ryuzakikami/bll_chess_game/docs/HausarbeitBLL/res/20250331_210004.jpg

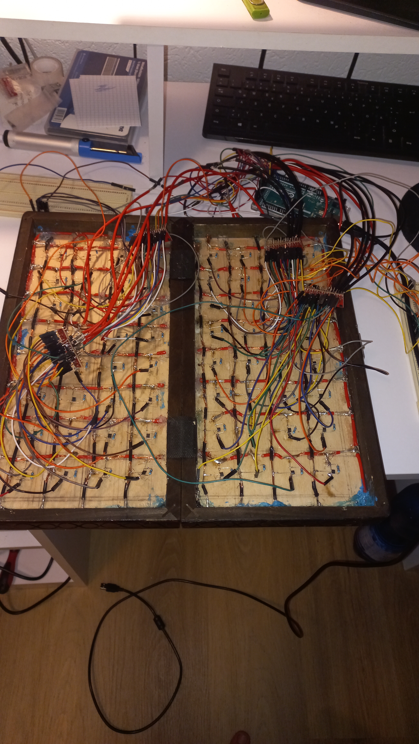
docs/HausarbeitBLL/res/20250331_210004.jpg
