ryuzakikami/bll_chess_game/docs/HausarbeitBLL/res/20250401_221237.jpg

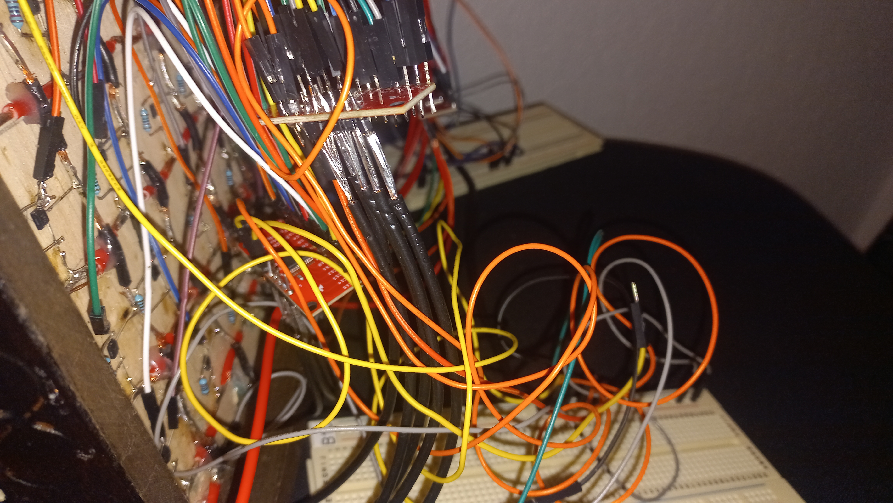
docs/HausarbeitBLL/res/20250401_221237.jpg
