ryuzakikami/bll_chess_game/docs/HausarbeitBLL/res/20250401_221310.jpg

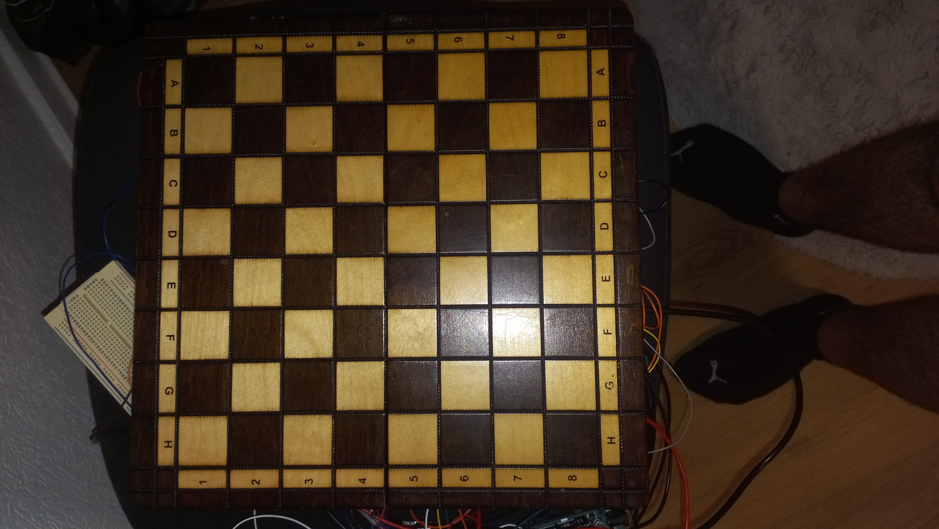
docs/HausarbeitBLL/res/20250401_221310.jpg
