ryuzakikami/bll_chess_game/docs/HausarbeitBLL/res/20250401_221319.jpg

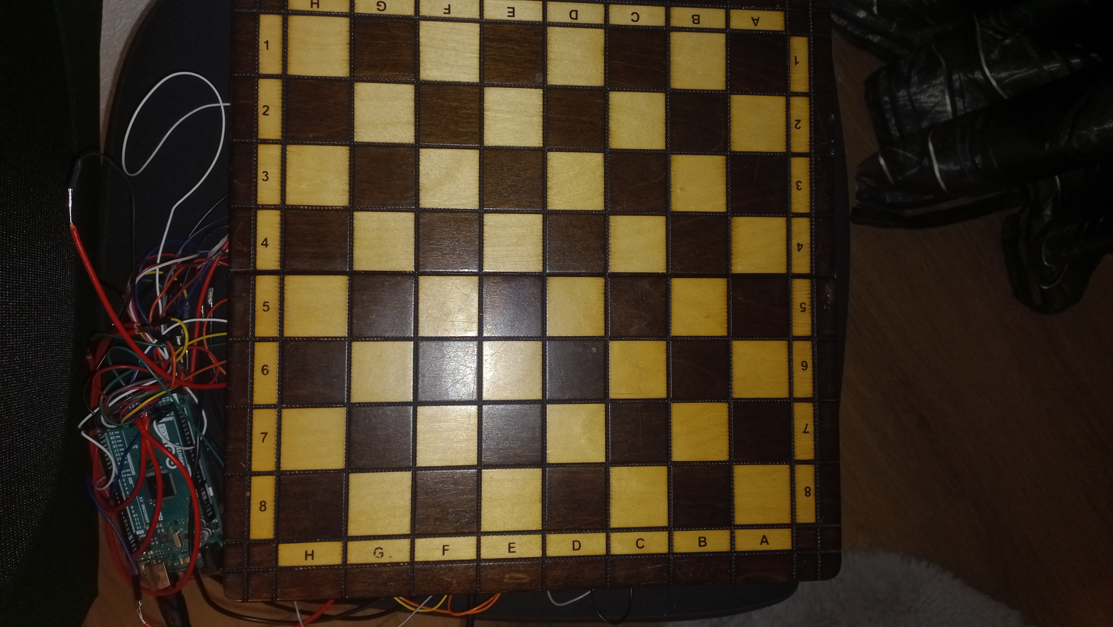
docs/HausarbeitBLL/res/20250401_221319.jpg
