ryuzakikami/bll_chess_game/docs/HausarbeitBLL/res/Elektronik/3144-Hall-Sensor.png

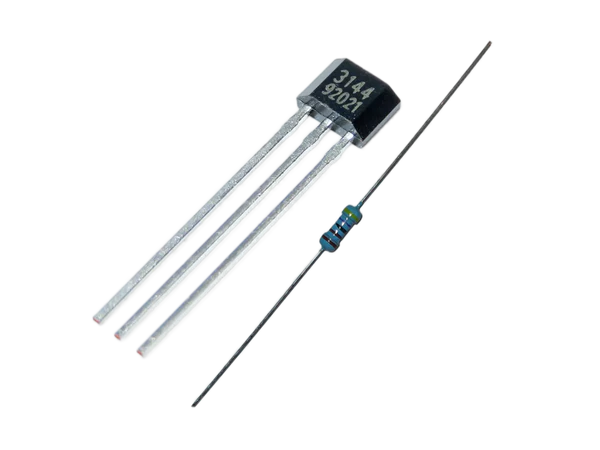
docs/HausarbeitBLL/res/Elektronik/3144-Hall-Sensor.png
