ryuzakikami/bll_chess_game/docs/HausarbeitBLL/res/Elektronik/Ardiono_mega_echt.png

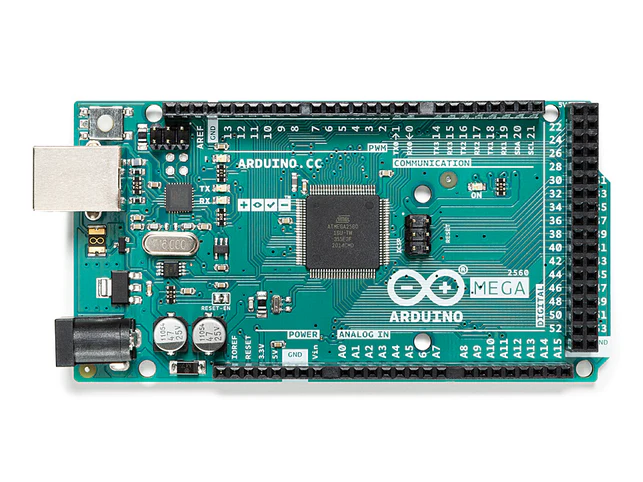
docs/HausarbeitBLL/res/Elektronik/Ardiono_mega_echt.png
