ryuzakikami/bll_chess_game/docs/HausarbeitBLL/res/Logic-Circuit-of-16-to-1-MUX.jpg.png

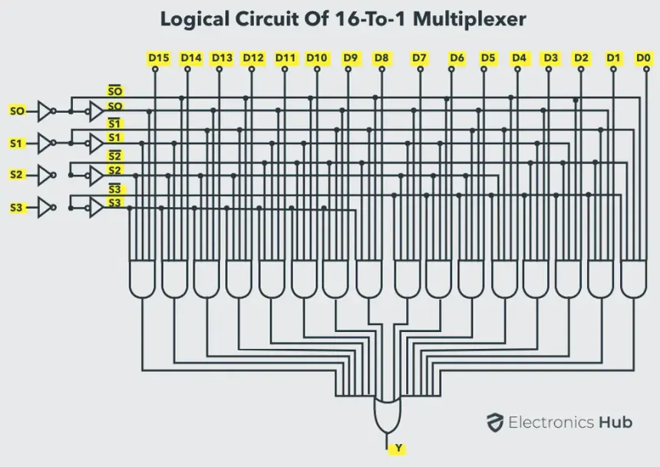
docs/HausarbeitBLL/res/Logic-Circuit-of-16-to-1-MUX.jpg.png
