ryuzakikami/bll_chess_game/docs/HausarbeitBLL/res/Vermessen.jpg

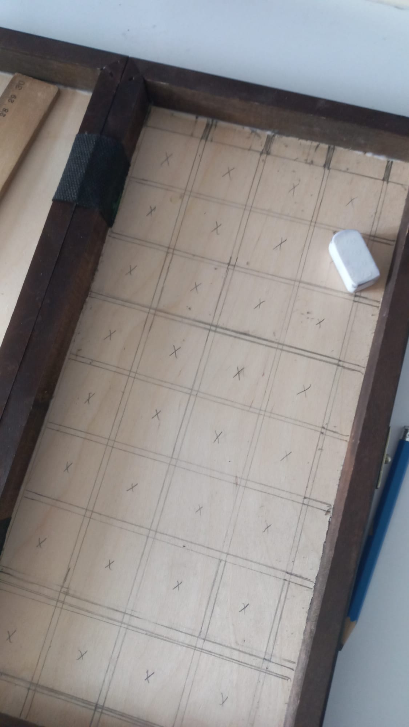
docs/HausarbeitBLL/res/Vermessen.jpg
