ryuzakikami/bll_chess_game/docs/schachbrett_model/Full Chess set (With 3D Board!) - 6810813/images/Untitled_7.png

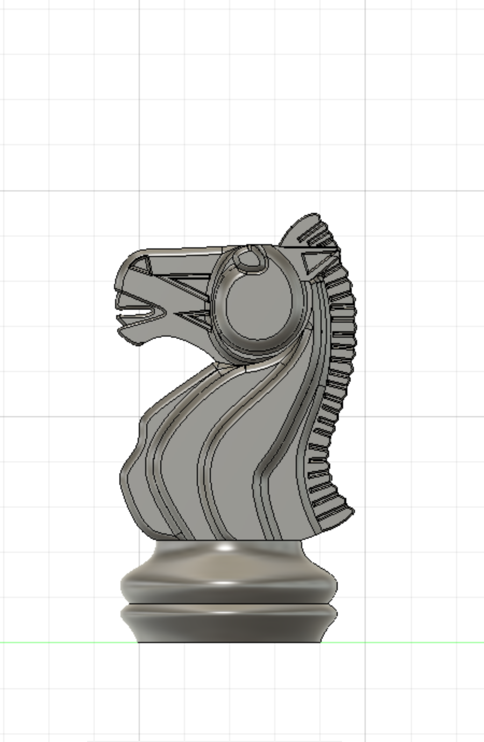
docs/schachbrett_model/Full Chess set (With 3D Board!) - 6810813/images/Untitled_7.png
