ryuzakikami/bll_chess_game/docs/HausarbeitBLL/res/20250401_213910.jpg

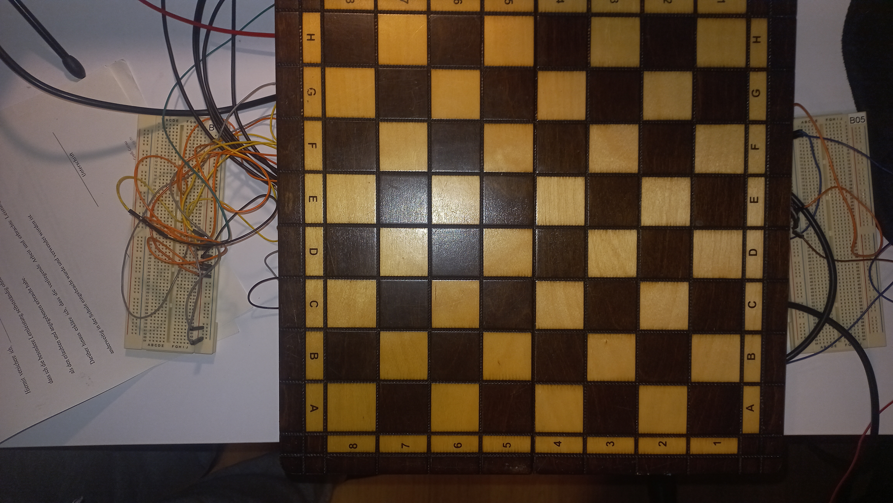
docs/HausarbeitBLL/res/20250401_213910.jpg
